akih-san/MEZW65C_RAM-Rev2.1G/reference data/HM678127UH-write.png

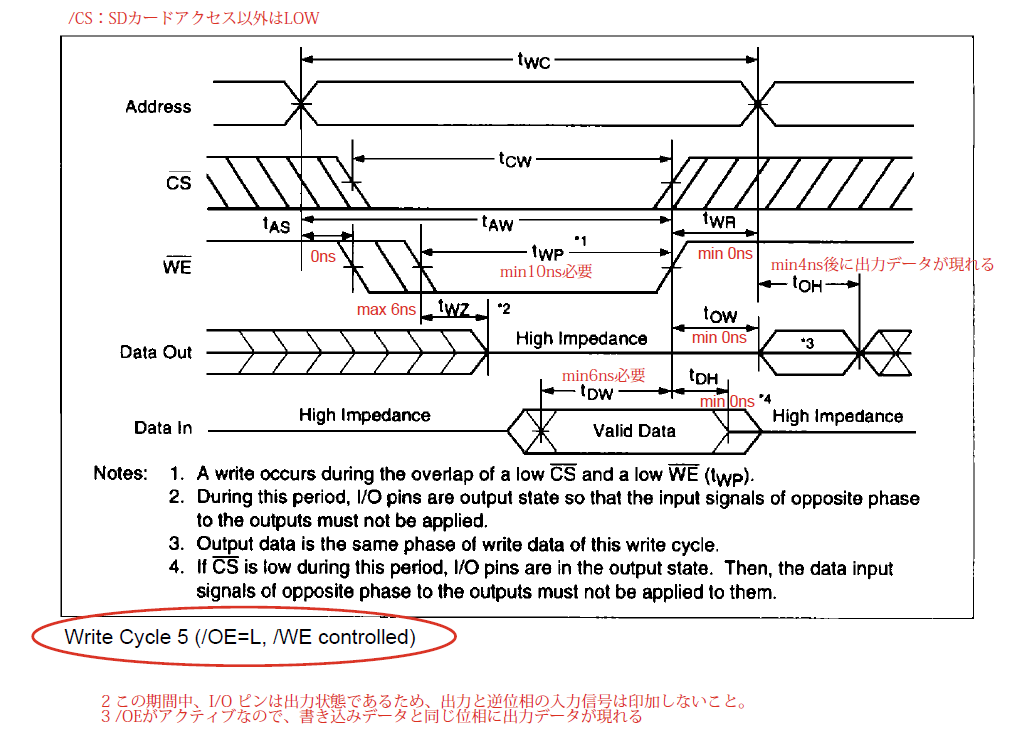
reference data/HM678127UH-write.png
