akih-san/MEZW65C_RAM-Rev2.1G/reference data/HM678127UH-真理値表.png

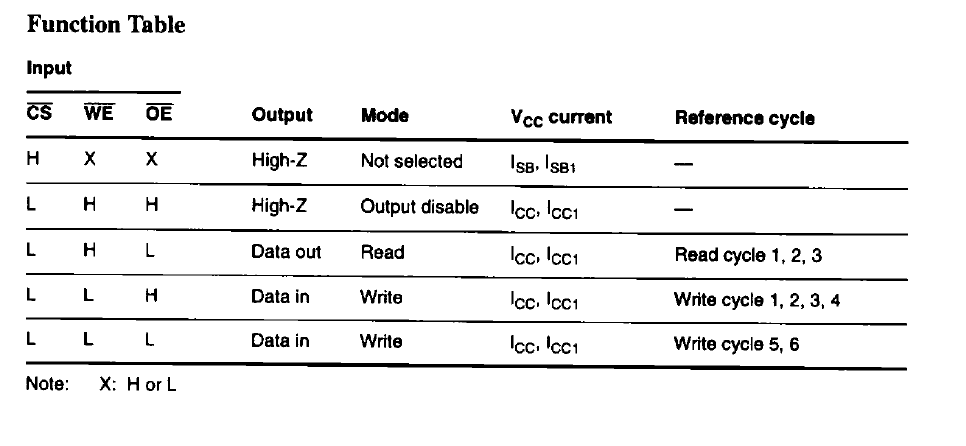
reference data/HM678127UH-真理値表.png
