akih-san/MEZW65C_RAM-Rev2.1G/reference data/w65c816_timing.png

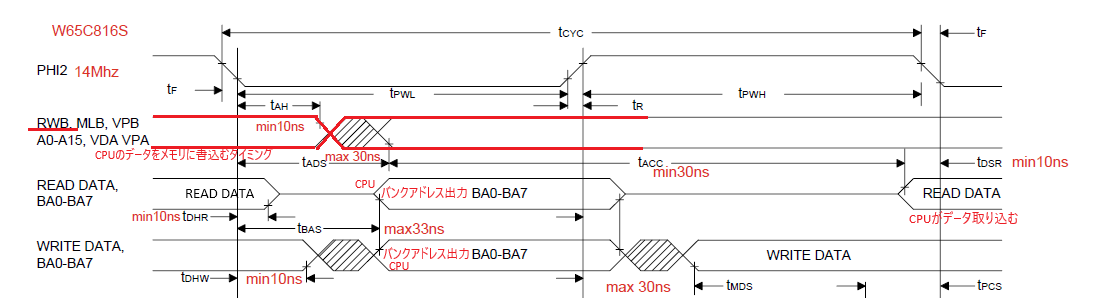
reference data/w65c816_timing.png
